zoolhilmi-coder/vseq/kicad_project/vseq.kicad_sch

## KiCad design kicad_project/vseq.kicad_sch (2026-07-07, an earlier design)

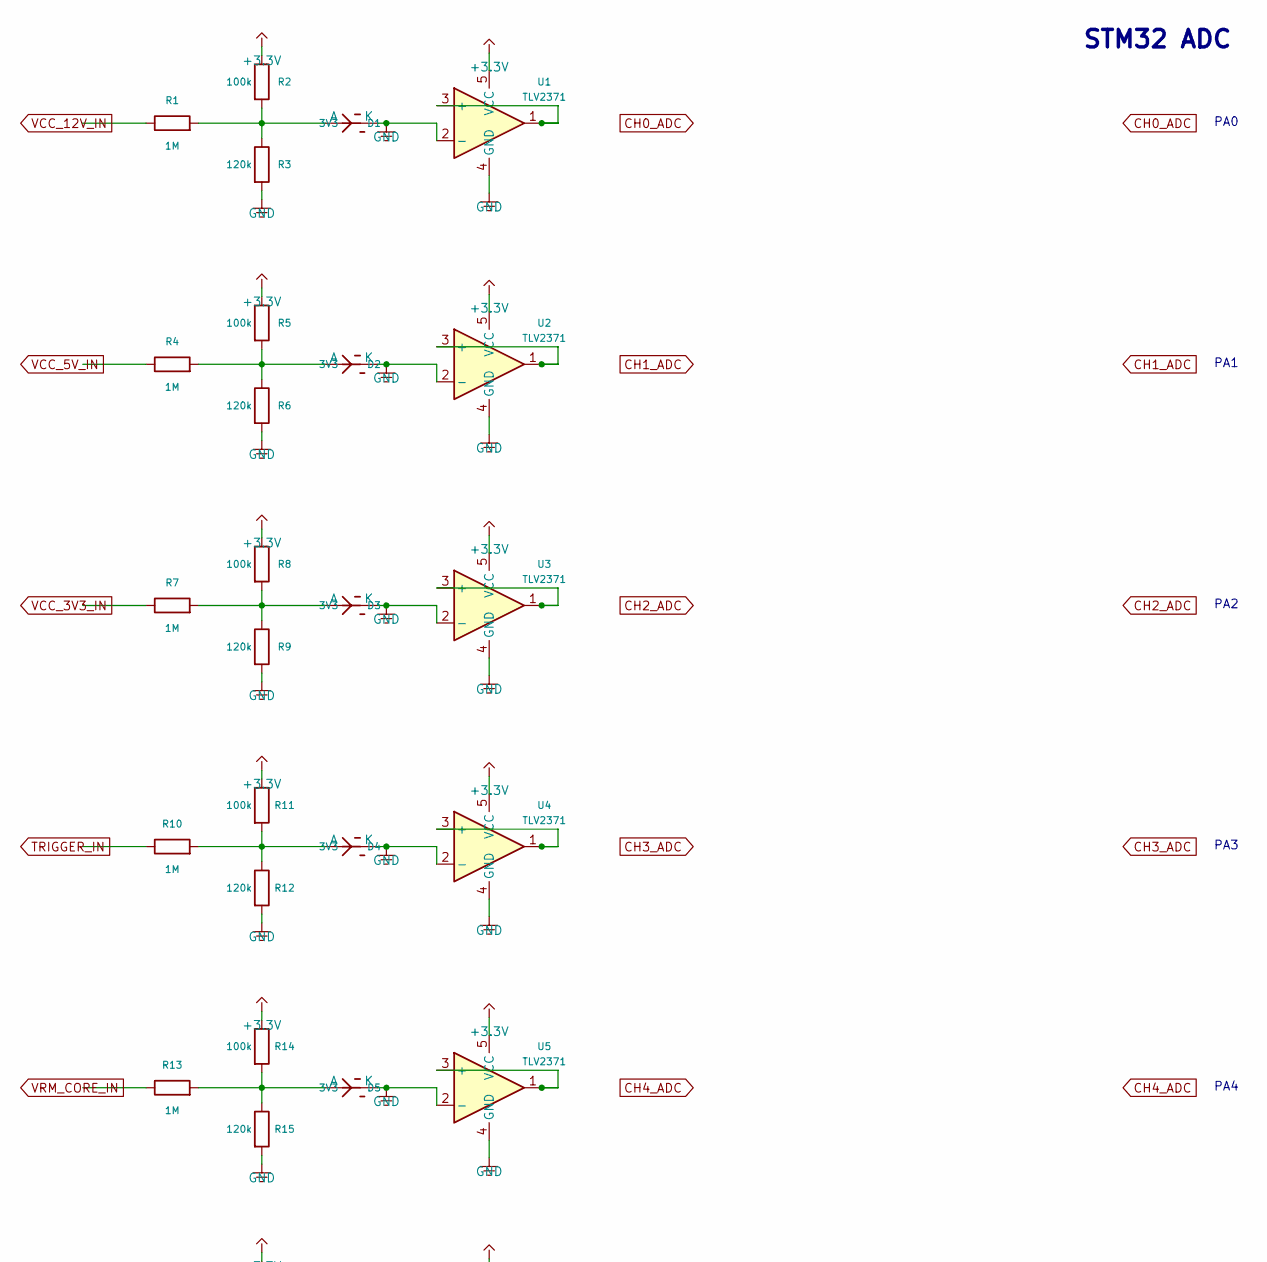
[picture p2: schematic vseq.kicad_sch, part in row 1, column 1]

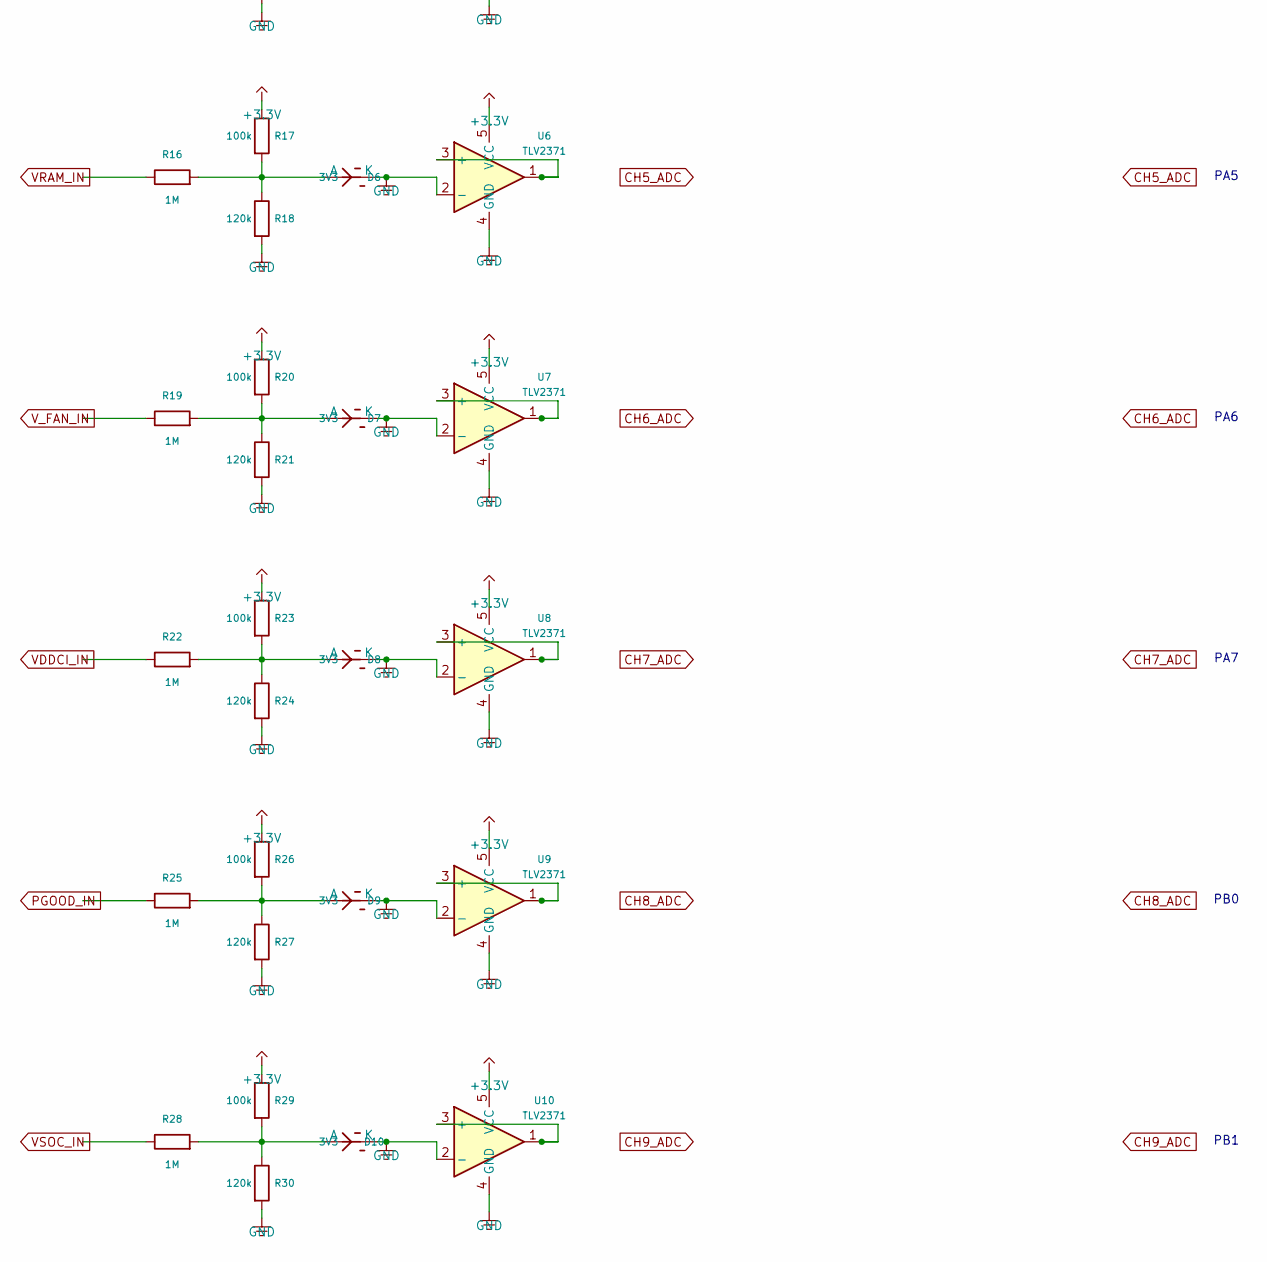
[picture p3: schematic vseq.kicad_sch, part in row 2, column 1]

Parts:
D1, D2, D3, D4, D5, D6, D7, D8, D9, D10: 3V3; D_SOD-123
R1, R4, R7, R10, R13, R16, R19, R22, R25, R28: 1M; R_0805_2012Metric
R2, R5, R8, R11, R14, R17, R20, R23, R26, R29: 100k; R_0805_2012Metric
R3, R6, R9, R12, R15, R18, R21, R24, R27, R30: 120k; R_0805_2012Metric
U1, U2, U3, U4, U5, U6, U7, U8, U9, U10: TLV2371; SOT-23-5

Connections:
+3.3V: R2.1, R5.1, R8.1, R11.1, R14.1, R17.1, R20.1, R23.1, R26.1, R29.1, U1.5 (VCC), U2.5 (VCC), U3.5 (VCC), U4.5 (VCC), U5.5 (VCC), U6.5 (VCC), U7.5 (VCC), U8.5 (VCC), U9.5 (VCC), U10.5 (VCC)
GND: D1.1 (K), D2.1 (K), D3.1 (K), D4.1 (K), D5.1 (K), D6.1 (K), D7.1 (K), D8.1 (K), D9.1 (K), D10.1 (K), R3.2, R6.2, R9.2, R12.2, R15.2, R18.2, R21.2, R24.2, R27.2, R30.2, U1.2 (-), U1.4 (GND), U2.2 (-), U2.4 (GND), U3.2 (-), U3.4 (GND), U4.2 (-), U4.4 (GND), U5.2 (-), U5.4 (GND), U6.2 (-), U6.4 (GND), U7.2 (-), U7.4 (GND), U8.2 (-), U8.4 (GND), U9.2 (-), U9.4 (GND), U10.2 (-), U10.4 (GND)
unnamed: D1.2 (A), R1.2, R2.2, R3.1
unnamed: D2.2 (A), R4.2, R5.2, R6.1
unnamed: D3.2 (A), R7.2, R8.2, R9.1
unnamed: D4.2 (A), R10.2, R11.2, R12.1
unnamed: D5.2 (A), R13.2, R14.2, R15.1
unnamed: D6.2 (A), R16.2, R17.2, R18.1
unnamed: D7.2 (A), R19.2, R20.2, R21.1
unnamed: D8.2 (A), R22.2, R23.2, R24.1
unnamed: D9.2 (A), R25.2, R26.2, R27.1
unnamed: D10.2 (A), R28.2, R29.2, R30.1
unnamed: U1.1, U1.3 (+)
unnamed: U2.1, U2.3 (+)
unnamed: U3.1, U3.3 (+)
unnamed: U4.1, U4.3 (+)
unnamed: U5.1, U5.3 (+)
unnamed: U6.1, U6.3 (+)
unnamed: U7.1, U7.3 (+)
unnamed: U8.1, U8.3 (+)
unnamed: U9.1, U9.3 (+)
unnamed: U10.1, U10.3 (+)

Notes on the sheet:
STM32 ADC
PA0
PA1
PA2
PA3
PA4
PA5
PA6
PA7
PB0
PB1
